HaroldMurcia/Channel_IoT/Documents/imagenes/PCB SRCA vistainferior.png

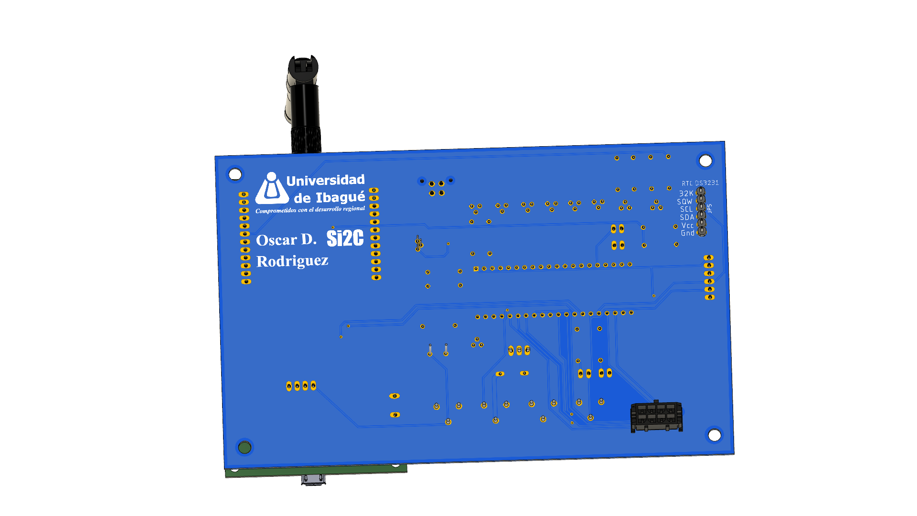
Documents/imagenes/PCB SRCA vistainferior.png
